g-vansh/vestor/docs/design/cad_room_pov.png

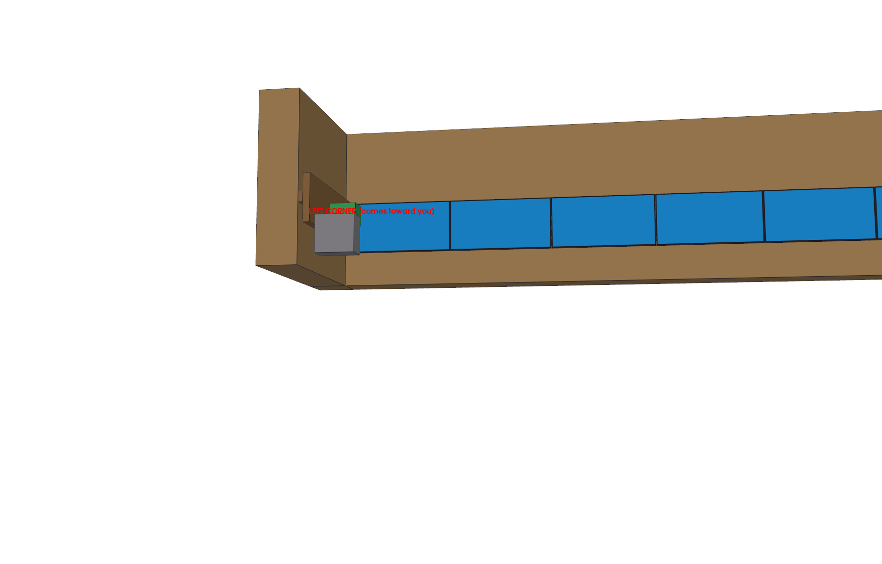
docs/design/cad_room_pov.png
