g-vansh/vestor/docs/design/cad_section.png

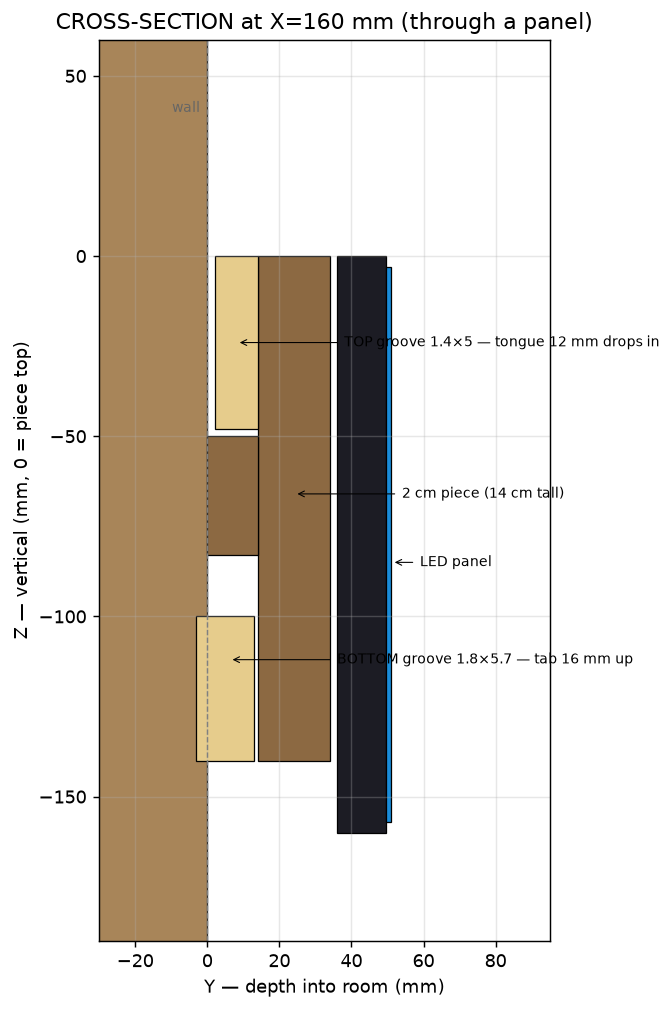
docs/design/cad_section.png
