g-vansh/vestor/docs/design/coupon_orientation.png

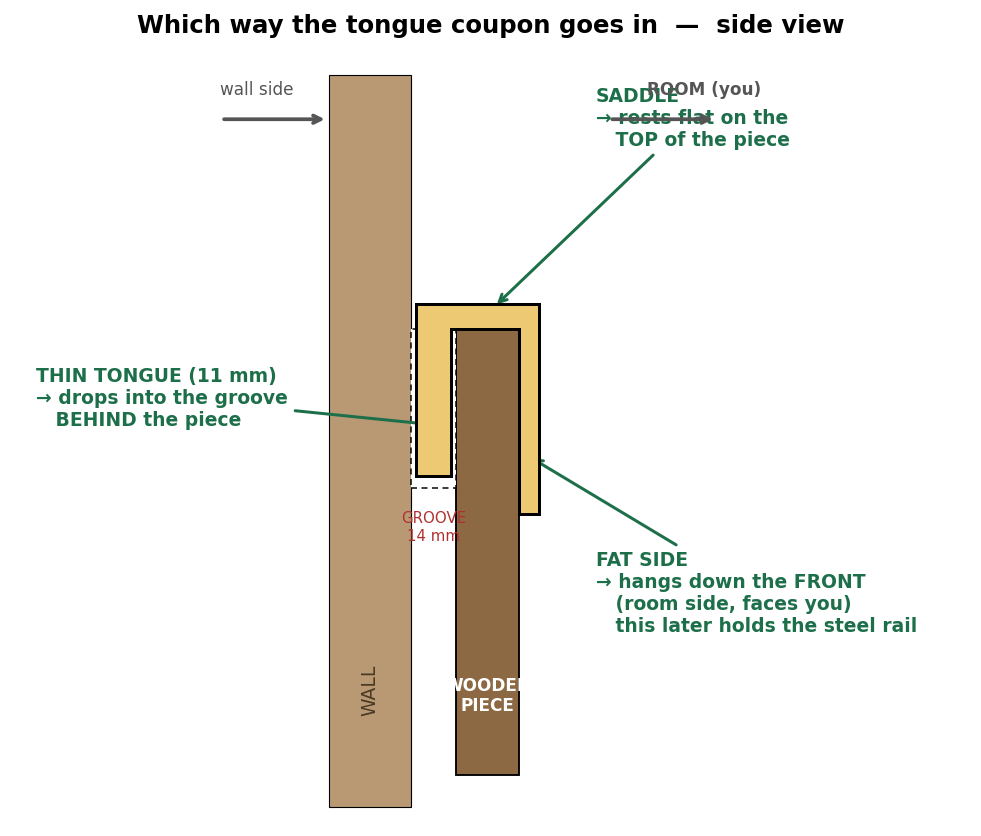
docs/design/coupon_orientation.png
