g-vansh/vestor/docs/design/part_cable_clip_fit.png

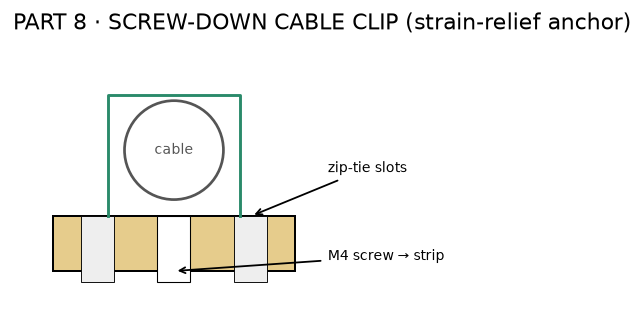
docs/design/part_cable_clip_fit.png
