g-vansh/vestor/docs/design/part_top_cleat_3d.png

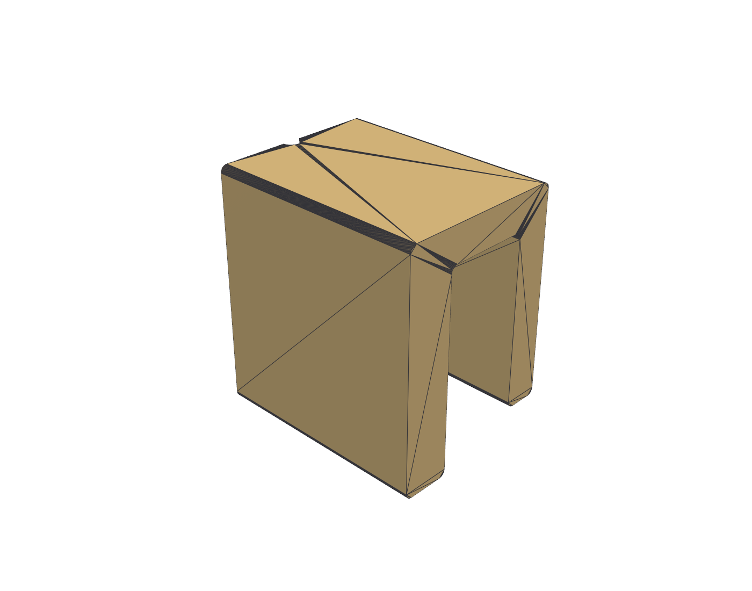
docs/design/part_top_cleat_3d.png
