g-vansh/vestor/docs/design/swoop_preview.png

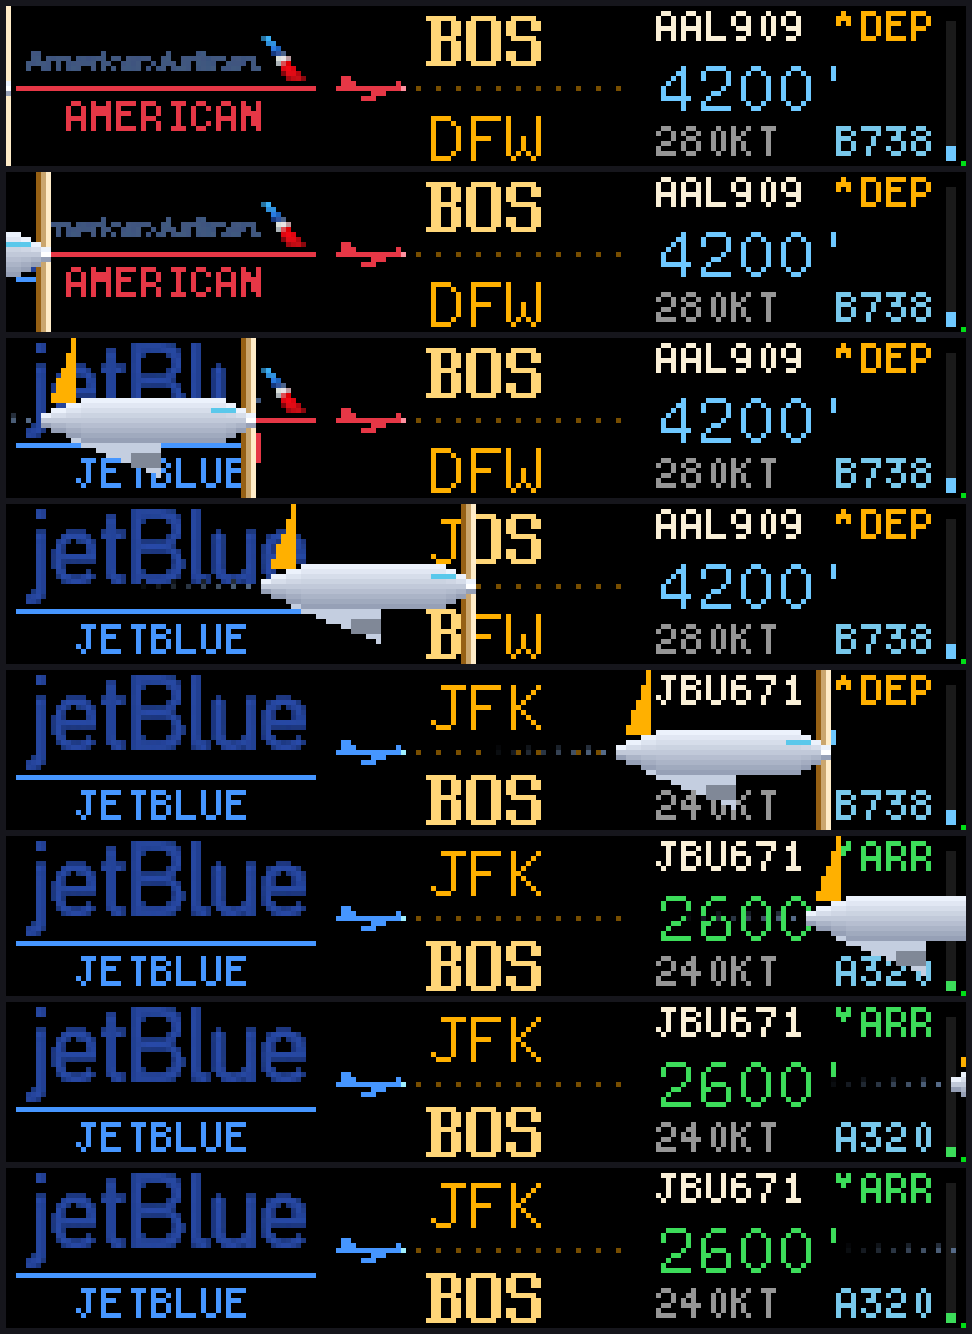
docs/design/swoop_preview.png
