g-vansh/vestor/docs/design/wall_top_profile.jpg

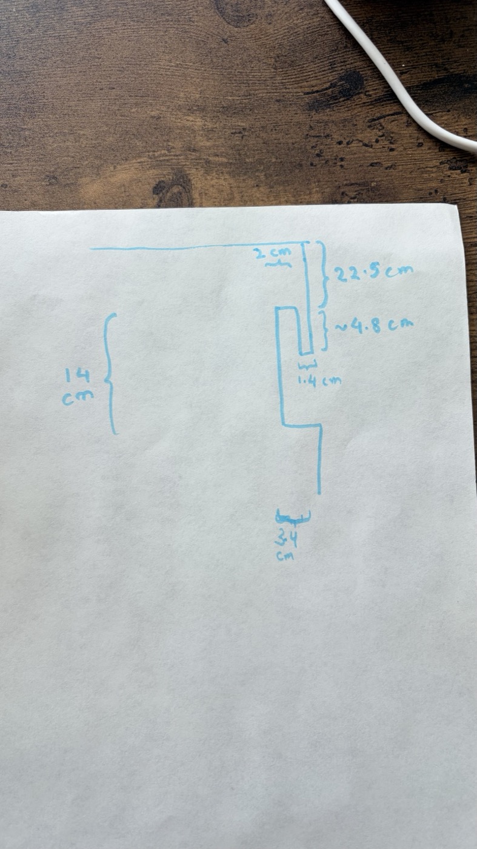
docs/design/wall_top_profile.jpg
