g-vansh/vestor/tools/preview_idle.png

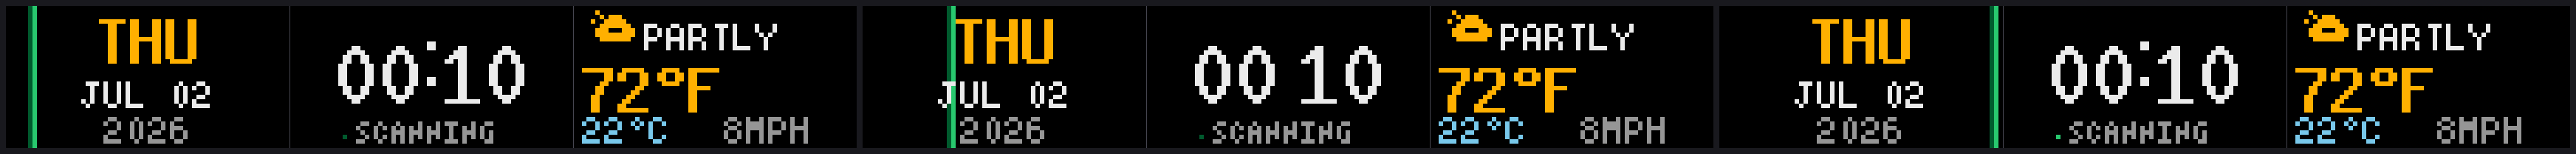
tools/preview_idle.png
